olsone/icetea/sound_tb.v

module test;
# test sn76489 on a memory bus

// Clocks

  reg clk100 = 0;
  reg clk12 = 0;
  reg clk44k = 0;
  reg sndclk = 0;
  
  always #5     clk100 = !clk100;  // half period
  // 12 MHz clock (ideal period 41.666 ns)  
  always begin // http://www.asic-world.com/verilog/timing_ctrl1.html
   #42 clk12 = !clk12;
   #41 clk12 = !clk12;
   #42 clk12 = !clk12;
   #42 clk12 = !clk12;
   #41 clk12 = !clk12;
   #42 clk12 = !clk12;
  end
  always #11337 clk44k = !clk44k; // half period of 44.1 KHz audio clock
  always #1118  sndclk = !sndclk; // half period of 447 kHz sndclk

  
  wire phi1, phi2, phi3, phi4;  
  wire memen, dbin, we, a15;
  
  // these events are for the mock classes (mem_read_gen, mem_write_gen). They trigger simulated CPU read or write cycles.
  reg read_request, write_request; 
  wire read_done, write_done;

  wire serclk, shld, adrin1, adrin2;
  reg reset;

  // simulated read cycle
  reg [15:0] address_from_cpu = 16'h8400;
  wire [15:0] address_bus; // internal wire to cru, memory mapped devices
  wire [7:0] data_bus;
  reg [15:0] data_word_read_by_cpu;
  reg [15:0] data_word_write_by_cpu;
  
  reg [15:0] expected_data;
  
  reg [4:0] tests_failed, tests_passed;
  event terminate_sim;
 
  reg [7:0] sndlist[37];
  integer i, j, len;
  integer duration;
  

  initial begin
    sndlist[0] = 8'h6;
    sndlist[1] = 8'h86;
    sndlist[2] = 8'h0D;
    sndlist[3] = 8'h97;
    sndlist[4] = 8'hAC;
    sndlist[5] = 8'h1A;
    sndlist[6] = 8'hB7;
    sndlist[7] = 8'h8;
    sndlist[8] = 8'h2;
    sndlist[9] = 8'h8F;
    sndlist[10] = 8'h8;
    sndlist[11] = 8'h2;
    sndlist[12] = 8'h2;
    sndlist[13] = 8'hAB;
    sndlist[14] = 8'h23;
    sndlist[15] = 8'h5;
    sndlist[16] = 8'h2;
    sndlist[17] = 8'h86;
    sndlist[18] = 8'h0D;
    sndlist[19] = 8'h4;
    sndlist[20] = 8'h1;
    sndlist[21] = 8'hBF;
    sndlist[22] = 8'h3;
    sndlist[23] = 8'h2;
    sndlist[24] = 8'h8E;
    sndlist[25] = 8'h0B;
    sndlist[26] = 8'h8;
    sndlist[27] = 8'h2;
    sndlist[28] = 8'h8A;
    sndlist[29] = 8'h0A;
    sndlist[30] = 8'h2;
    sndlist[31] = 8'h3;
    sndlist[32] = 8'hAC;
    sndlist[33] = 8'h1A;
    sndlist[34] = 8'hB7;
    sndlist[35] = 8'h8;
    sndlist[36] = 0;

    $dumpfile("test.vcd");
    $dumpvars(0,test);
    tests_failed = 0;
    tests_passed = 0;
    clk100 = 0;
    clk12 = 0;
    clk44k = 0;
    read_request = 0;
    write_request = 0;
    expected_data = 16'haa55;
    
    i = 0;
    while(sndlist[i]) begin
      len = sndlist[i];
      i++;
      
      for (j=0; j < len; j++) begin
        data_word_write_by_cpu[15:8] = sndlist[i++];
        write_request = 1;
        # 10 write_request = 0;
        wait(write_done);
      end
    
      duration = sndlist[i++];
      for (j=0; j<duration; j++) begin
        # 16666666; // 1/60th second
      end
    end
    
    # 50 -> terminate_sim;
  end
  
  
  // Assert that write cycle was correct
  always @(posedge write_done) begin
    if (data_word_write_by_cpu[15:8] == data_bus[7:0]) begin
      $display("pass Memory Write Cycle");
      tests_passed <= tests_passed + 1;
    end
    else begin
      $display("FAIL Memory Write Cycle. Expected value %2h, but data_bus=%4h", data_word_write_by_cpu[15:8], data_bus);
      tests_failed <= tests_failed + 1;
    end
  end
  

  // Termination Message  
  always @(terminate_sim)  begin
   $display ("Terminating simulation");
   if (tests_passed == 2 && tests_failed == 0) begin
     $display ("Simulation Result : PASSED");
   end
   else begin
     $display ("Simulation Result : FAILED");
     $display ("tests passed: %d", tests_passed);
     $display ("tests failed: %d", tests_failed);
     
   end
   $display ("###################################################");
   #1 $finish;
  end

  // test it in memory_interface
  // Sources:
  clockgen     phases(clk12, phi1, phi2, phi3, phi4);
  shift74ls165 test1 (clk100, address_from_cpu[15:8], shld, serclk, adrin1);
  shift74ls165 test2 (clk100, address_from_cpu[7:0], shld, serclk, adrin2);
  mem_read_gen genread(read_request, phi2, data_bus, data_word_read_by_cpu, memen_rd, dbin, a15, read_done);
  // with mem_write_gen and memory_interface (mem_read_gen not at issue),
  // memory_interface_tb.v:19: vvp.tgt error: (implicit) uwire "data_bus" must have a single driver, found (2).
  // Cured by changing data_bus to inout in mem_write_gen.
  mem_write_gen genwrite(write_request, phi1, phi2, phi3, data_bus, data_word_write_by_cpu, memen_wr, we, a15, write_done);
  
  // module under test:
  wire [2:0] state;
  assign memen = memen_rd && memen_wr;
  wire  [15:0] data_pins_in;
  wire  [15:0] data_pins_out;
  wire  [17:0] address_pins;
  // SRAM enable lines
  wire OE_pin, WE_pin, CS_pin;
  wire data_pins_out_en;
  // TODO:  memory mock SRAM
  assign data_pins_in = expected_data;

  // cru and memory mapper
  // how to get the decoded cru address on time? 400 ns max from addr valid to cruin valid.
  reg cruclk, cruout, cruin;
  
  wire [3:0] bank_sel;
  wire [6:0] bank_address;
  wire bank_readonly, bank_mapped;
  // memory mapped devices
  wire mm_enable;
  
  cru_interface cru(
    .clk(clk100), .cruclk(cruclk), .memen(memen), .cru_address(address_bus[13:1]), .cruout(cruout), .cruin(cruin), 
    .bank_sel(bank_sel), .bank_mapped(bank_mapped), .bank_readonly(bank_readonly), .bank_address(bank_address)
  );

  // FORTi card
  wire [7:0] sample;
  wire sound_enable = memen || address_bus[15:10] != 6'b100001 || a15; // active low
  wire sound_cs1 = sound_enable || address_bus[1]; // active low
  wire sound_cs2 = sound_enable || address_bus[2];
  wire sound_cs3 = sound_enable || address_bus[3];
  wire sound_cs4 = sound_enable || address_bus[4];
  wire [7:0] sample1, sample2, sample3, sample4;
  wire [9:0] counter1;
  wire bit1;
  sn76489 sound1(.cs(sound_cs1), .clk(sndclk), .data_bus(data_bus), .we(we), .sample(sample1), .bit1(bit1), .counter1(counter1)); 
  sn76489 sound2(.cs(sound_cs2), .clk(sndclk), .data_bus(data_bus), .we(we), .sample(sample2)); 
  sn76489 sound3(.cs(sound_cs3), .clk(sndclk), .data_bus(data_bus), .we(we), .sample(sample3)); 
  sn76489 sound4(.cs(sound_cs4), .clk(sndclk), .data_bus(data_bus), .we(we), .sample(sample4));
  reg [9:0] mixer;
  assign mixer = sample1 + sample2 + sample3 + sample4;
  
  // cs can go to x when a15=z, right after memen low, when the addr bus is not yet valid.
  // this is ok. the address and a15 are stable before we goes low.
  
  memory_interface mem(
    // Host control lines and memory bus
    .clk(clk100), .phi3(phi3), .data_bus(data_bus), .address_bus(address_bus), .memen(memen), .dbin(dbin), .we(we), .a15(a15), 
    // Serial interface for address bus
    .shld(shld), .serclk(serclk), .adrin1(adrin1), .adrin2(adrin2), 
    // test bench monitoring only
    .state(state),
    // SRAM pins
    .data_pins_out_en(data_pins_out_en), .address_pins(address_pins), .data_pins_in(data_pins_in), .data_pins_out(data_pins_out),
    .OE(OE_pin), .WE(WE_pin), .CS(CS_pin),
    // memory mapper
    .bank_sel(bank_sel), .bank_mapped(bank_mapped), .bank_readonly(bank_readonly), .bank_address(bank_address),
    // memory mapped devices
    .mm_enable(mm_enable)
    );
  integer file;

  initial
    file = $fopenw("sample1.wav"); 

//  initial  
//    $monitor("At time %t, req=%d/%d memen=%d we=%d addr=%4x a15=%d dbus=%2h, cs=%d cs2=%d", 
//      $time, write_request, write_done, memen, we, address_bus, a15, data_bus, sound_cs1, sound_cs2);

  initial
    $monitor("time=%t sample1=%d", $time, sample1);

  always @(clk44k) $fputc(sample1, file);

endmodule // test
