olsone/icetea/mem_read_gen.v

module mem_read_gen(read_request, phi2, data_bus, data_word, memen, dbin, a15, read_done, o_state);
  // Mock generate memory read cycle signals
  //
  // caller must:
  // assign we = and(memen_read, memen_write) (active low)
  
  input read_request;
  input  phi2;
  output memen, dbin, a15, read_done;
  output reg [15:0] data_word;
  input wire[7:0] data_bus; 
  output wire [2:0] o_state;
  
//  wire phi2;
  reg [2:0] state;
//  wire  memen, dbin, a15, done;
  wire a15_lo, a15_hi;

    

  // states
  // 0 read_request received, waiting for phi3
  // 1 read begin
  // 2,3 wait states
  // 4 read ms byte begin
  // 5,6 wait states
  // 7 read done
  assign o_state = state;
  
  initial begin
    state = 7;
  end

  assign memen =  (state == 0 || state == 7);
  assign dbin  = !(state == 0 || state == 7);
  assign a15_hi   = (state == 1 || state == 2 || state == 3);
  assign a15_lo   = (state == 4 || state == 5 || state == 6);
  assign read_done  = (state == 7);  
  assign a15 = a15_hi ? 1 : (a15_lo ? 0 : 1'bz);
  
  always @(posedge read_request) 
  begin
    state = 0;
  end

  always @(posedge phi2) 
  begin
    if (state != 0 && state != 7) begin
      if (!a15)
        data_word[7:0] = data_bus;
      else
        data_word[15:8] = data_bus;
    end  
    if (state != 7) state = state + 1;
      
  end


  endmodule // clockgen
